Halflink/inqdoLogo/FreeCad/neopixelbracket_I.FCStd

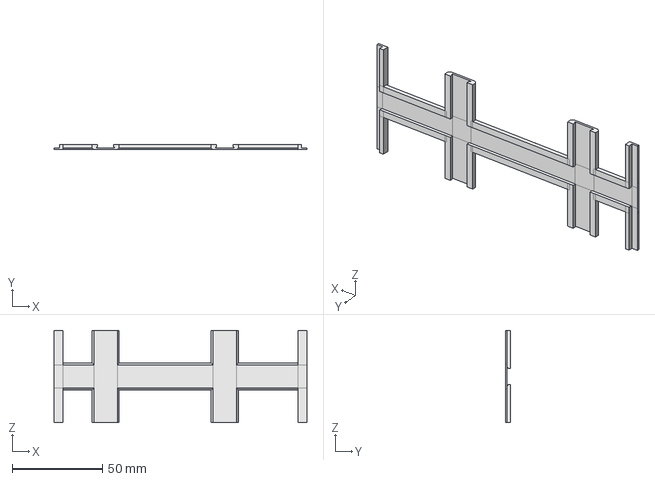
[picture p12: CAD file, 2023-08-24]
FreeCad/neopixelbracket_I.FCStd
140.0 x 3.00 x 51.0 mm
