Halflink/inqdoLogo/FreeCad/neopixelbracket.FCStd

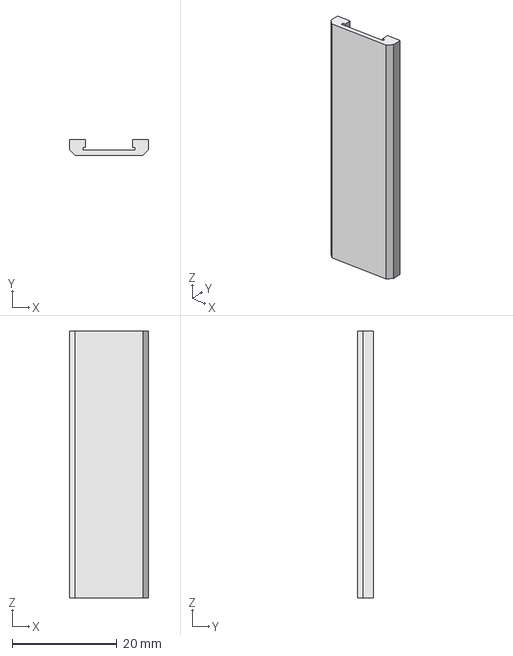
[picture p13: CAD file, 2023-08-03]
FreeCad/neopixelbracket.FCStd
15.0 x 3.00 x 51.0 mm
