Halflink/inqdoLogo/FreeCad/picoBracket_v2.FCStd

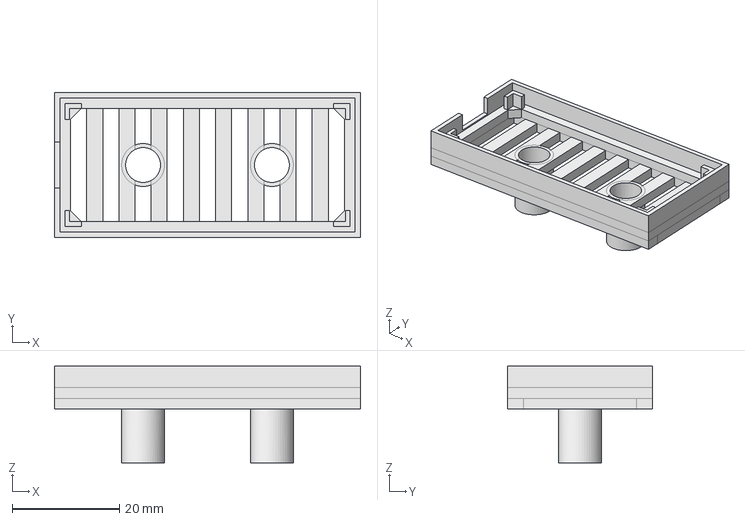
[picture p14: CAD file, 2023-08-03]
FreeCad/picoBracket_v2.FCStd
57.0 x 27.0 x 18.0 mm
