Halflink/inqdoLogo/FreeCad/frameTubeType2.FCStd

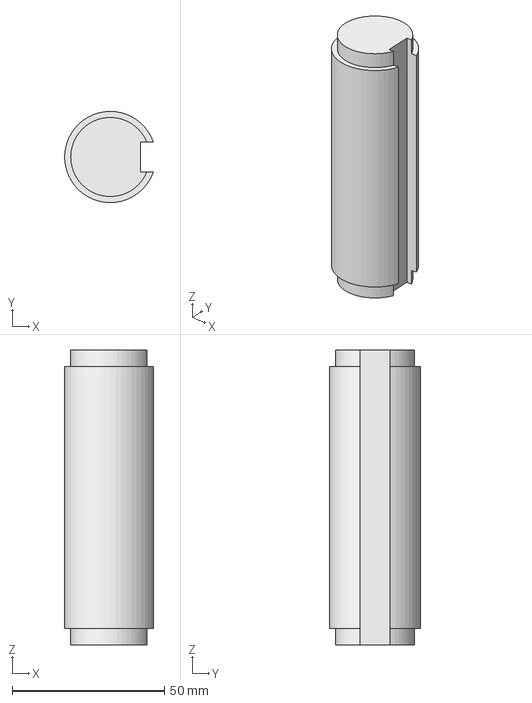
[picture p15: CAD file, 2023-07-04]
FreeCad/frameTubeType2.FCStd
29.1 x 30.0 x 97.0 mm
