Halflink/inqdoLogo/FreeCad/frameMofType2.FCStd

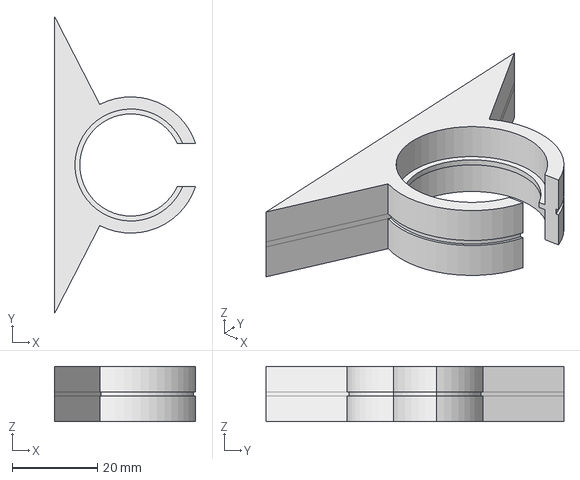
[picture p16: CAD file, 2023-07-02]
FreeCad/frameMofType2.FCStd
33.2 x 70.0 x 13.0 mm
