Halflink/inqdoLogo/FreeCad/frameMof.FCStd

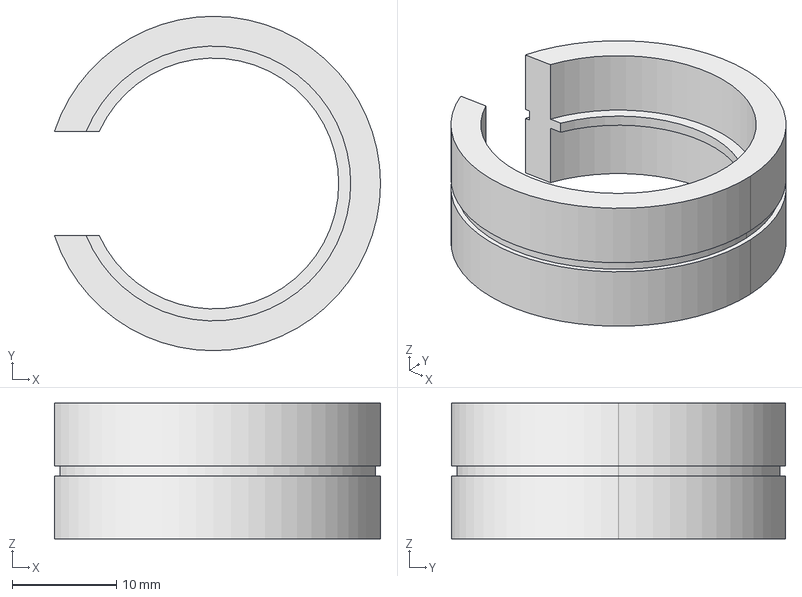
[picture p17: CAD file, 2023-07-02]
FreeCad/frameMof.FCStd
31.2 x 32.0 x 13.0 mm
