Halflink/inqdoLogo/FreeCad/inqdoLogo.FCStd

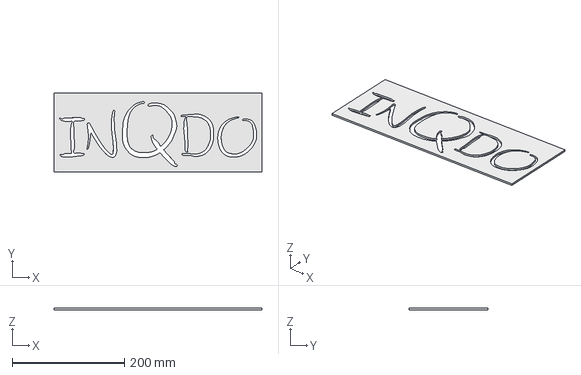
[picture p18: CAD file, 2023-07-02]
FreeCad/inqdoLogo.FCStd
370.0 x 140.0 x 3.00 mm
