Halflink/inqdoLogo/FreeCad/frameTubeType3.FCStd

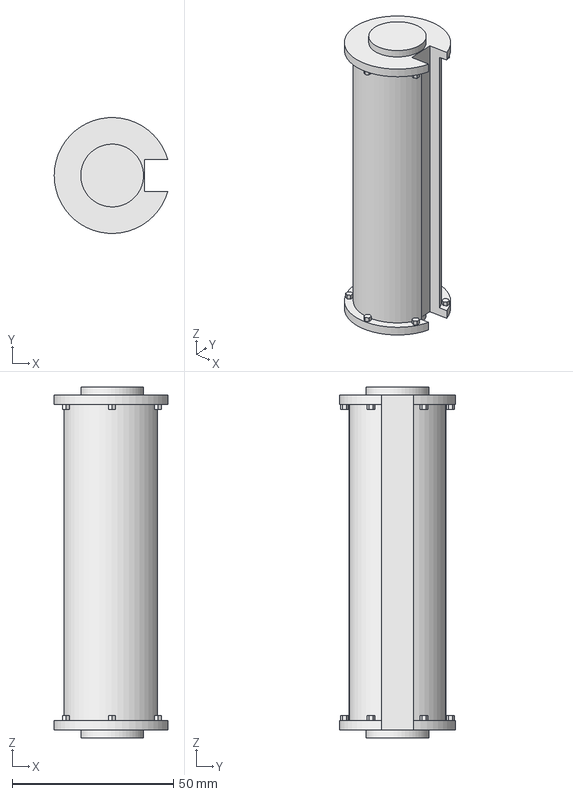
[picture p19: CAD file, 2023-07-01]
FreeCad/frameTubeType3.FCStd
35.3 x 36.0 x 109.0 mm
