Halflink/inqdoLogo/FreeCad/frameCorner.FCStd

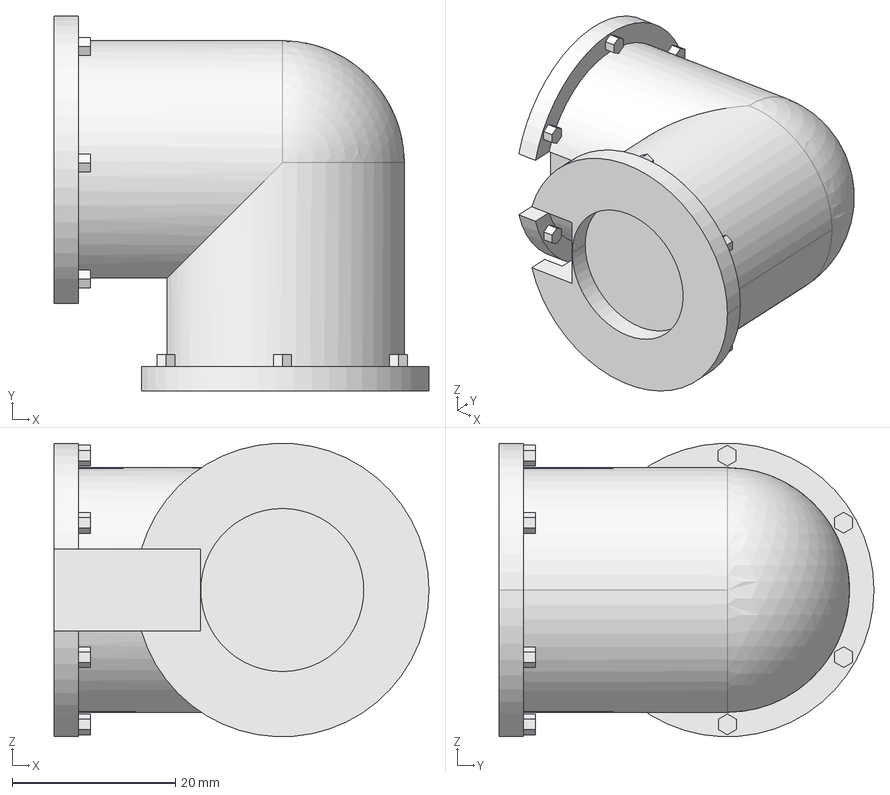
[picture p20: CAD file, 2023-06-30]
FreeCad/frameCorner.FCStd
46.0 x 46.0 x 36.0 mm
