Halflink/inqdoLogo/FreeCad/frameTubeType1.FCStd

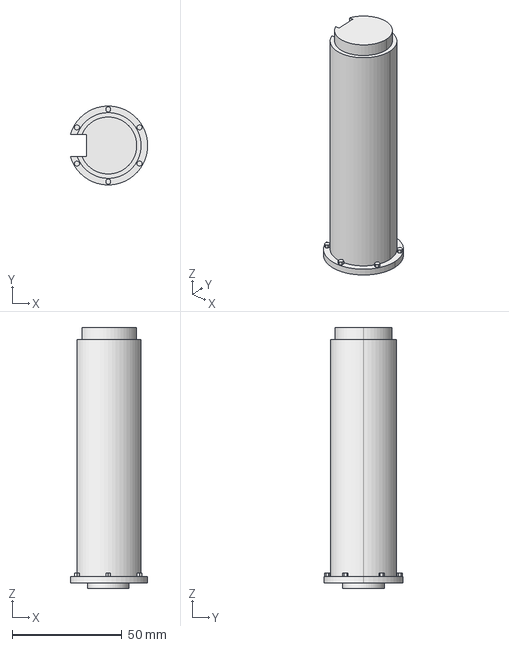
[picture p21: CAD file, 2023-06-30]
FreeCad/frameTubeType1.FCStd
35.3 x 36.0 x 119.0 mm
